BoujeeEnjinia1701/bridgepulse/cad/drawings/BRP-DWG-001.pdf

CONCEPT, NOT FOR FABRICATION | BridgePulse · github.com/BoujeeEnjinia1701/bridgepulse

FRONT VIEW

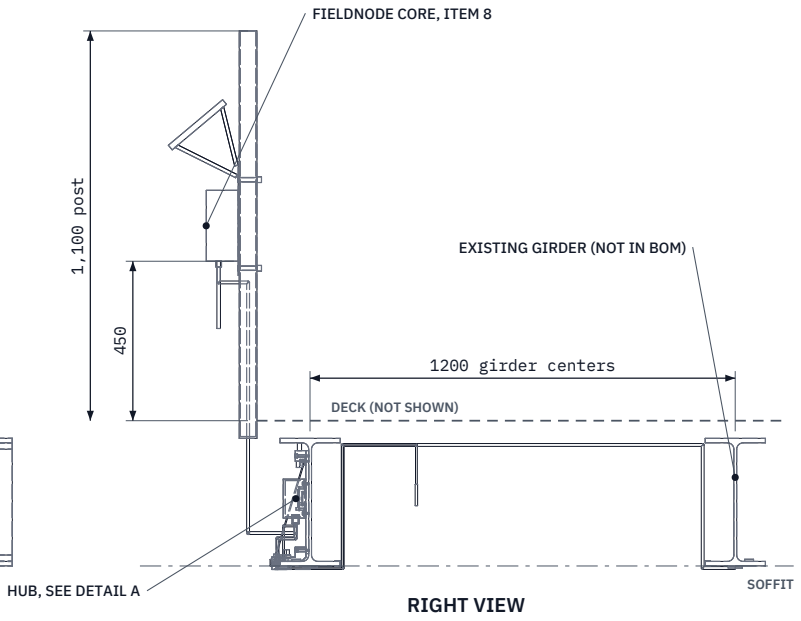
[picture p7: figure]
RIGHT VIEW; SOFFIT; DECK (NOT SHOWN); 1200 girder centers; 1,100 post; FIELDNODE CORE, ITEM 8; EXISTING GIRDER (NOT IN BOM); HUB, SEE DETAIL A

Scale 1:20; looking at the front (along +Y)

Scale 1:20; looking at the right side (along -X)

DETAIL A: HUB ON SOUTH GIRDER
Right view, scale 1:4

### PRELIMINARY, NOT FOR FABRICATION

MIDSPAN

DECK AND HANDRAILS OMITTED FOR CLARITY; HUB AND FIELDNODE ON THE -Y (SOUTH) SIDE

159

LANYARD GIRDER CLAMP, ITEM 4

3 MM STAINLESS WIRE LANYARD

291 plate

190 hub center

72

CLAMP JAW, 10 BELOW SOFFIT

HUB, ITEMS 1 TO 3

PLATE, ITEM 4

M12 JACK SCREW

LANYARD PAD EYE

ISOMETRIC VIEW
Not to scale; deck omitted; seen from the front right and above, about 30 deg elevation

MAIN DIMENSIONS AND INTERFACES (MM)
Hub 170 x 64 x 110 IP67, 9 inside the flange tip line
Plate 200 x 291 x 8 Al on the web, 22 clear of flanges; no drilling
Foot clamps +/-76; M12 jack; lanyard clamp at -275, 159 clear
Gauge covers under each flange at midspan; 10 max below soffit (R9: 15) FieldNode on the post, base 450 above deck; M12 5-pin, RS-485, 5 V Probes (item 6) TMP1826 class, 7 dia sheaths; steel on flange, air in shade Example girders IPE 360 class at 1200 centers, span 6,400
Third-angle; front view from -Y; 800 segment at midspan (x = 0)
REV | DESCRIPTION | DATE | BY
P1 | Preliminary GA for TRL 3 (from cad/src/model.py) | 2026-09-25 | AC
P2 | Probe note per BRP-DDR-002 | 2026-09-25 | AC
P3 | Far gauge cable clear of bottom flanges per BRP-DDR-003 | 2026-09-27 | AC
P4 | Layout and labels tidied | 2026-09-30 | AC
P5 | Made constructable per BRP-DDR-004 | 2026-09-30 | AC
P6 | Lanyard, pad eye and girder clamp per BRP-DEC-001 | 2026-10-02 | AC
BRIDGEPULSE | github.com/BoujeeEnjinia1701/bridgepulse

## General arrangement at midspan

DRAWING NO.
BRP-DWG-001

REV
P6

SHEET
1 of 1

SIZE

## ANSI B

SCALE
1:20

UNITS
mm
PROJECTION | DATE
2026-10-02

DRAWN
Amish Chadha

MATERIAL / NOTES
6061 Al plate; bought-in parts per bom/bom.csv. PRELIMINARY, NOT FOR FABRICATION
Licensed CERN-OHL-S-2.0 · Design Molecule Lab · designmolecule.com | Generated from cad/src; do not edit by hand
