BoujeeEnjinia1701/bridgepulse/cad/drawings/BRP-DWG-101.pdf

BUILD PLAN SKETCH, PLAN NOT YET BUILT BridgePulse · github.com/BoujeeEnjinia1701/bridgepulse

FRONT VIEW
Scale 1:5; looking at the front (along +Y)

TOP VIEW
Scale 1:5; looking down (along -Z)

RIGHT VIEW
Scale 1:5; looking at the right side (along -X)

200

8 291

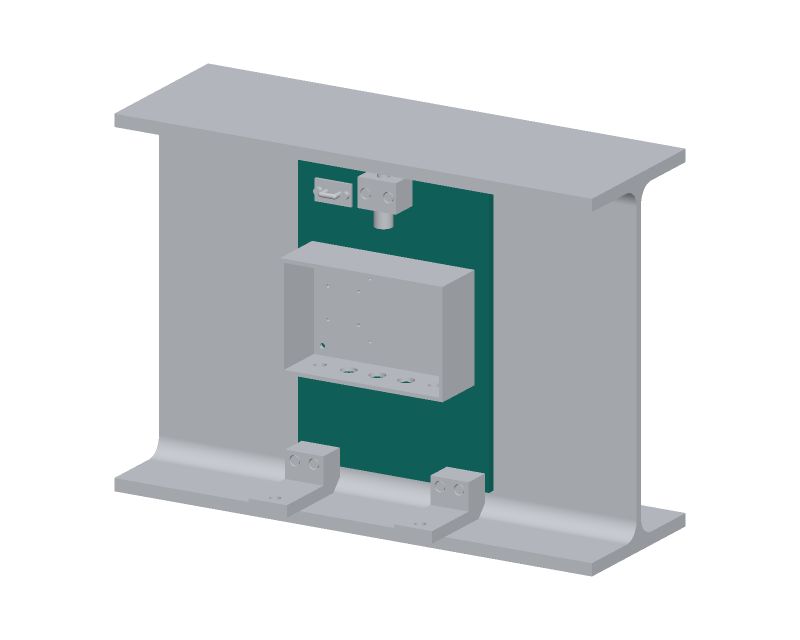
[picture p8: figure]

WHERE IT GOES
This part in colour, its neighbours in grey

HOW TO MAKE IT AND HOW IT FITS
Blank 200 x 290.6 x 8 mm: the girder's clear web height
(334.6 mm on IPE 360) less 22 mm at each end, to clear the root fillets. Front face: the face the hub sits on. Heights from the bottom edge, sideways from the centre line. All holes go right through.
Hub screws: four M5 tapped (drill 4.2) at 72 each side,
113.3 and 197.3 up.
Foot block screws: four M6 tapped (drill 5.0) at 66 and 86 each side, 9 up.
Jack block screws: two M6 tapped at 12 each side, 275.6 up. Pad eye screws: two M5 tapped at 48 and 76 left of centre,
260.6 up (left side only).
Deburr; break the edges 0.5 mm; hard anodize (it also insulates).
Check: lay the foot blocks and jack block on it and look through each hole.
REV | DESCRIPTION | DATE | BY
P1 | Making sketch for the prototype build plan | 2026-09-30 | AC
P2 | Pad eye holes replace the lanyard hole (BRP-DEC-001) | 2026-10-02 | AC
BRIDGEPULSE | github.com/BoujeeEnjinia1701/bridgepulse

## BridgePulse mounting plate: making sketch

DRAWING NO.
BRP-DWG-101

REV
P2

SHEET
1 of 1

SIZE

## ANSI B

SCALE
1:5

UNITS
mm
PROJECTION | DATE
2026-10-02

DRAWN
Amish Chadha

MATERIAL / NOTES
6061 aluminium plate 8 mm, hard anodized after machining
Licensed CERN-OHL-S-2.0 · Design Molecule Lab · designmolecule.com | Generated from cad/src; do not edit by hand
