BoujeeEnjinia1701/bridgepulse/cad/drawings/BRP-DWG-102.pdf

BUILD PLAN SKETCH, PLAN NOT YET BUILT BridgePulse · github.com/BoujeeEnjinia1701/bridgepulse

FRONT VIEW
Scale 1:2; looking at the front (along +Y)

TOP VIEW
Scale 1:2; looking down (along -Z)

RIGHT VIEW
Scale 1:2; looking at the right side (along -X)

40

96 40

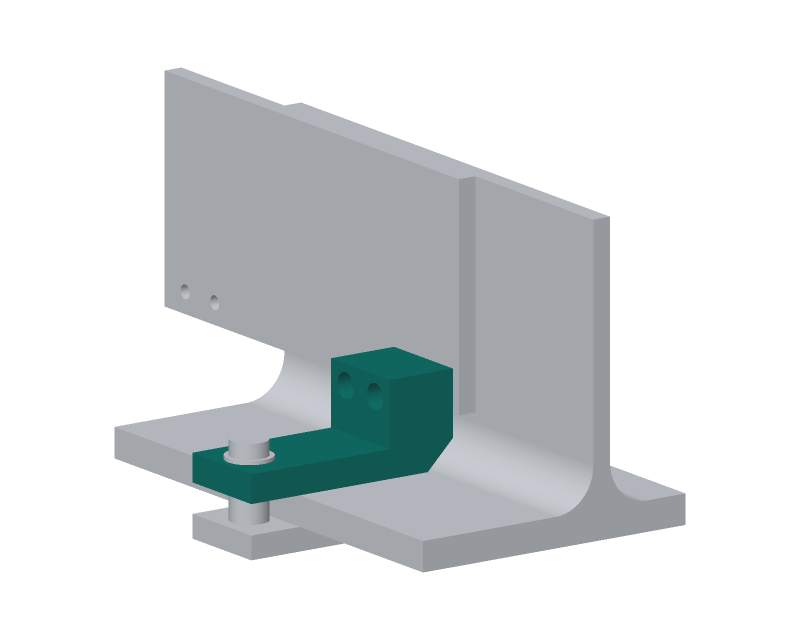
[picture p43: figure]

WHERE IT GOES
This part in colour, its neighbours in grey

HOW TO MAKE IT AND HOW IT FITS
Make two, both the same. Saw a 40 mm slice off 100 x 40 mm bar and square it to 96 long, 40 tall and 40 wide.
Saw out a step 66 long and 28 deep, leaving a tall end 30 long and
a tail 12 thick. The tall end's back face goes on the plate.
File a 12 x 12 mm 45 degree chamfer along the bottom of the back face: it keeps the block off the girder's root fillet.
Tall end: two 6.6 mm holes through, 10 each side of centre, 31 up; counterbore 11 mm, 6.5 deep, from the front for M6 cap screws.
Tail: one 11 mm hole, 13 from its end, on the centre line.
Fit: back face flat on the plate front, bottom on the flange top, tail out past the flange tip. Two M6 x 30 screws into the plate. Check: on a flange offcut it sits flat with no rock at the fillet.
REV | DESCRIPTION | DATE | BY
P1 | Making sketch for the prototype build plan | 2026-09-30 | AC
BRIDGEPULSE | github.com/BoujeeEnjinia1701/bridgepulse

## BridgePulse foot block (make 2): making sketch

DRAWING NO.
BRP-DWG-102

REV
P1

SHEET
1 of 1

SIZE

## ANSI B

SCALE
1:2

UNITS
mm
PROJECTION | DATE
2026-09-30

DRAWN
Amish Chadha

MATERIAL / NOTES
6061 aluminium flat bar 100 x 40 mm, hard anodized
Licensed CERN-OHL-S-2.0 · Design Molecule Lab · designmolecule.com | Generated from cad/src; do not edit by hand
