BoujeeEnjinia1701/bridgepulse/cad/drawings/BRP-DWG-103.pdf

BUILD PLAN SKETCH, PLAN NOT YET BUILT BridgePulse · github.com/BoujeeEnjinia1701/bridgepulse

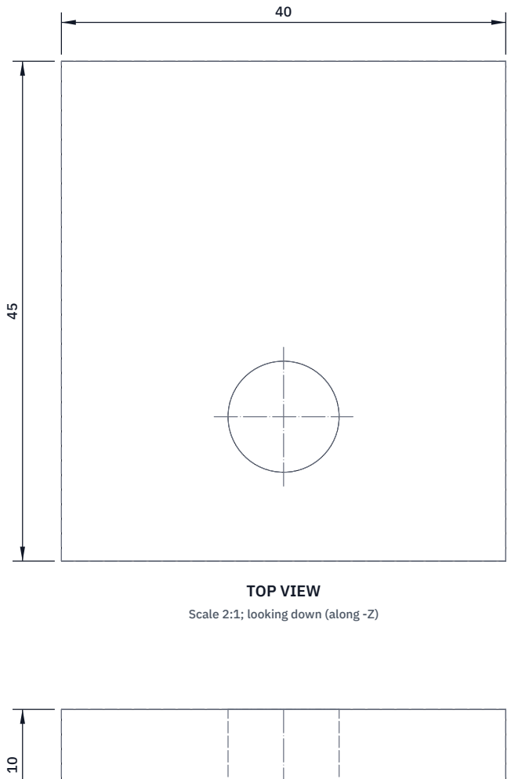
[picture p44: figure]
TOP VIEW; Scale 2:1; looking down (along -Z)

FRONT VIEW
Scale 2:1; looking at the front (along +Y)

RIGHT VIEW
Scale 2:1; looking at the right side (along -X)

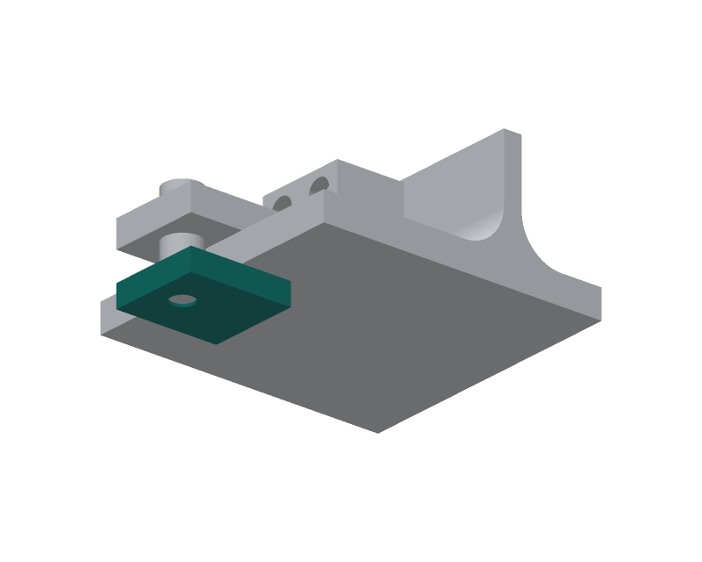
[picture p45: figure]

WHERE IT GOES
This part in colour, its neighbours in grey

HOW TO MAKE IT AND HOW IT FITS
Jaw: cut two 45 mm lengths of 40 x 10 mm steel flat bar; deburr.
Drill 8.5 mm and tap M10 right through, 13 from one end, on the centre line. Break the edges; zinc plate or paint with zinc-rich primer.
Packer: cut two lengths of steel tube, 16 mm outside, 10.5 mm or more inside, 12.2 long: the flange thickness less 0.5 mm.
Measure the real flange first and cut to suit; square the ends.
Fit: the jaw goes under the flange, 22 mm in from the tip, its tapped end out past the tip. The packer stands on the jaw beside the tip. The M10 x 35 bolt comes down through the foot block tail and the packer into the jaw; it must not stand out below the jaw.
Check: the bolt runs into the jaw by hand, and its tip stops
1 mm or more short of the jaw's underside.
REV | DESCRIPTION | DATE | BY
P1 | Making sketch for the prototype build plan | 2026-09-30 | AC
BRIDGEPULSE | github.com/BoujeeEnjinia1701/bridgepulse

## BridgePulse clamp jaw and packer (make 2 each): making sketch

DRAWING NO.
BRP-DWG-103

REV
P1

SHEET
1 of 1

SIZE

## ANSI B

SCALE
2:1

UNITS
mm
PROJECTION | DATE
2026-09-30

DRAWN
Amish Chadha

MATERIAL / NOTES
Steel flat bar 40 x 10 mm, zinc plated; packer: steel tube 16 mm outside
Licensed CERN-OHL-S-2.0 · Design Molecule Lab · designmolecule.com | Generated from cad/src; do not edit by hand
