BoujeeEnjinia1701/bridgepulse/cad/drawings/BRP-DWG-104.pdf

BUILD PLAN SKETCH, PLAN NOT YET BUILT BridgePulse · github.com/BoujeeEnjinia1701/bridgepulse

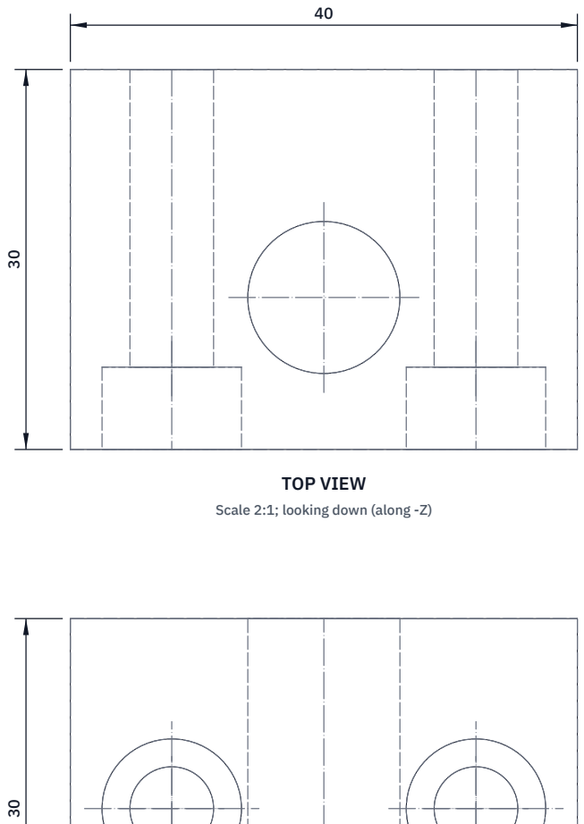
[picture p46: figure]
TOP VIEW; Scale 2:1; looking down (along -Z)
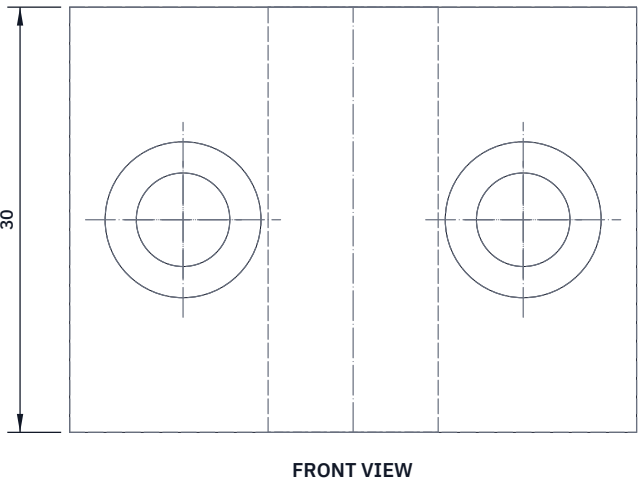
[picture p47: figure]
FRONT VIEW

Scale 2:1; looking at the front (along +Y)

RIGHT VIEW
Scale 2:1; looking at the right side (along -X)

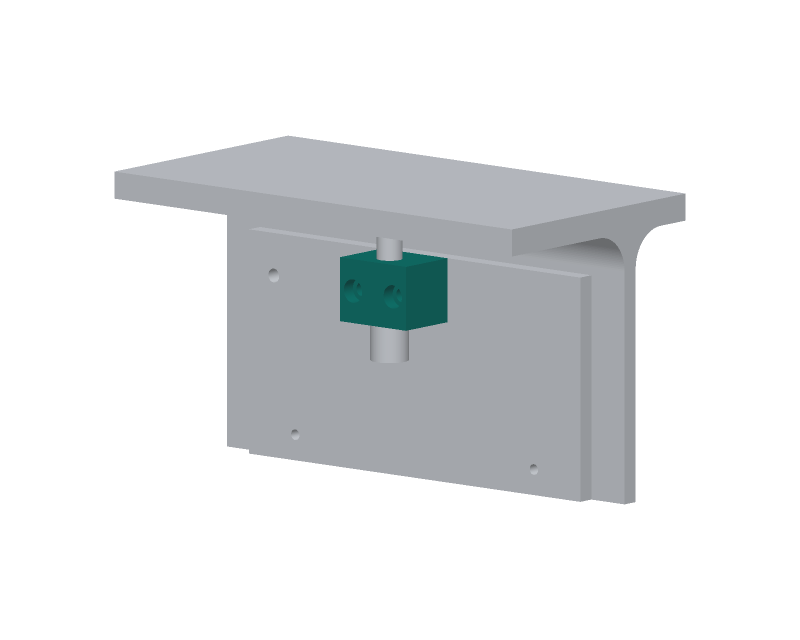
[picture p48: figure]

WHERE IT GOES
This part in colour, its neighbours in grey

HOW TO MAKE IT AND HOW IT FITS
Cut 30 mm off 40 x 30 mm bar: a block 40 wide, 30 deep, 30 tall.
The 40 x 30 face that goes on the plate is the back face.
Jack hole: drill 10.2 mm top to bottom, 18 from the back face, on the centre line, square to the top; tap M12 the full 30 mm.
Fixing holes: two 6.6 mm holes front to back, 12 each side of centre,
half way up; counterbore 11 mm, 6.5 deep, from the front.
Fit: back face on the plate front, top flush with the plate's top edge; two M6 x 30 cap screws into the plate.
The M12 x 70 jack screw goes up through it, head below, lock nut under the block; its end bears on the top flange 22 mm above. Check: the jack screw turns freely through the full thread.
REV | DESCRIPTION | DATE | BY
P1 | Making sketch for the prototype build plan | 2026-09-30 | AC
BRIDGEPULSE | github.com/BoujeeEnjinia1701/bridgepulse

## BridgePulse jack block: making sketch

DRAWING NO.
BRP-DWG-104

REV
P1

SHEET
1 of 1

SIZE

## ANSI B

SCALE
2:1

UNITS
mm
PROJECTION | DATE
2026-09-30

DRAWN
Amish Chadha

MATERIAL / NOTES
6061 aluminium flat bar 40 x 30 mm
Licensed CERN-OHL-S-2.0 · Design Molecule Lab · designmolecule.com | Generated from cad/src; do not edit by hand
