BoujeeEnjinia1701/bridgepulse/cad/drawings/BRP-DWG-105.pdf

BUILD PLAN SKETCH, PLAN NOT YET BUILT BridgePulse · github.com/BoujeeEnjinia1701/bridgepulse

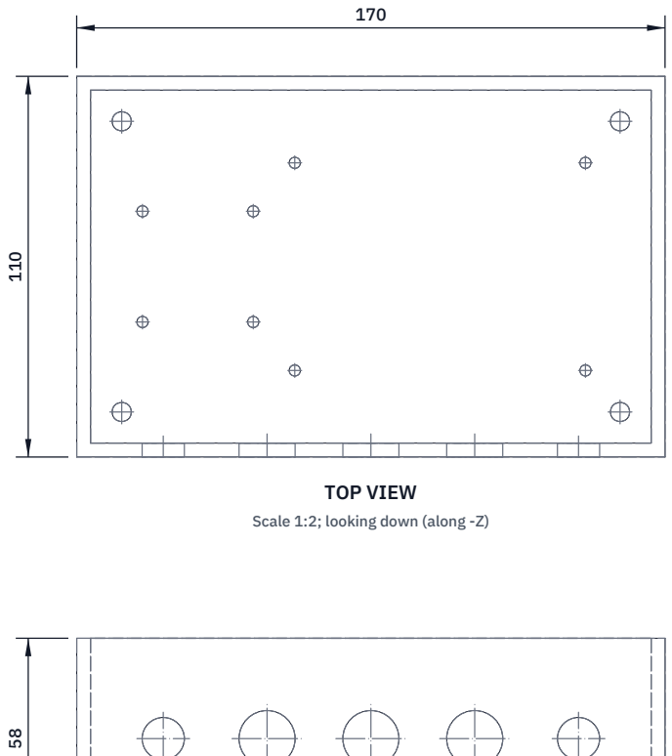
[picture p49: figure]
TOP VIEW; Scale 1:2; looking down (along -Z)

FRONT VIEW
Scale 1:2; looking at the front (along +Y)

RIGHT VIEW
Scale 1:2; looking at the right side (along -X)

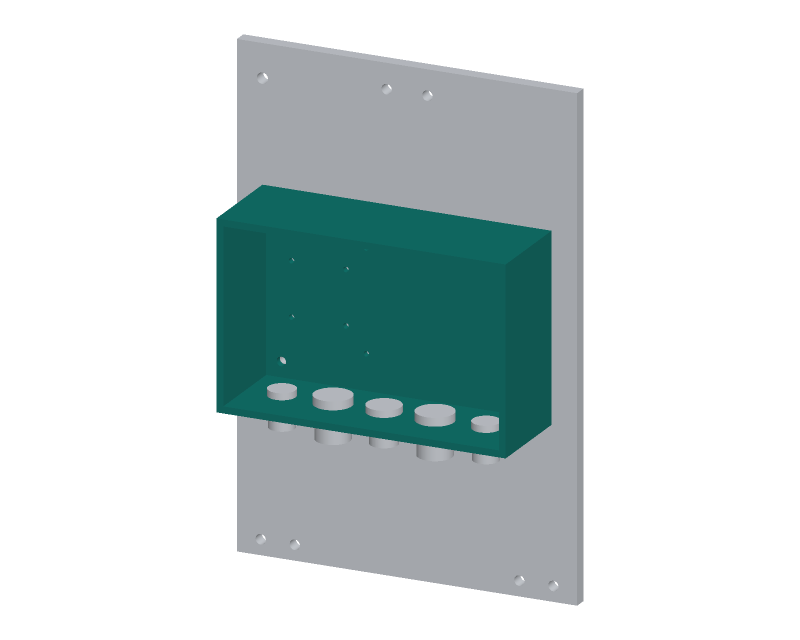
[picture p50: figure]

WHERE IT GOES
This part in colour, its neighbours in grey

HOW TO MAKE IT AND HOW IT FITS
Drawn lying on its back with the lid off: the top view looks into the box
at the base; the front view shows the bottom face.
Base, from the base's centre: four 5.5 mm holes at 72 each side, 42 above and below (the hub screws).
Base: eight 3.2 mm holes for the board spacers and standoffs, countersunk outside so the M3 heads sit flush (positions in the hub holes picture). Bottom face, on its centre line, sideways from the centre:
60 left: 12.5 mm (steel probe gland, M12)
30 left and 30 right: 16.5 mm (gauge glands, M16)
centre: 16.5 mm (M12 panel connector, M16 thread)
60 right: 12.5 mm (air probe gland, M12). Left and right as seen from the lid. Deburr inside and out; clean the lid gasket groove of chips.
REV | DESCRIPTION | DATE | BY
P1 | Making sketch for the prototype build plan | 2026-09-30 | AC
BRIDGEPULSE | github.com/BoujeeEnjinia1701/bridgepulse

## BridgePulse hub enclosure: drilling sketch

DRAWING NO.
BRP-DWG-105

REV
P1

SHEET
1 of 1

SIZE

## ANSI B

SCALE
1:2

UNITS
mm
PROJECTION | DATE
2026-09-30

DRAWN
Amish Chadha

MATERIAL / NOTES
Bought die-cast aluminium box, IP67, 170 x 64 x 110 mm
Licensed CERN-OHL-S-2.0 · Design Molecule Lab · designmolecule.com | Generated from cad/src; do not edit by hand
