BoujeeEnjinia1701/bridgepulse/cad/drawings/BRP-DWG-106.pdf

BUILD PLAN SKETCH, PLAN NOT YET BUILT BridgePulse · github.com/BoujeeEnjinia1701/bridgepulse

FRONT VIEW
Scale 2:1; looking at the front (along +Y)

TOP VIEW
Scale 2:1; looking down (along -Z)

RIGHT VIEW
Scale 2:1; looking at the right side (along -X)

40

25 6

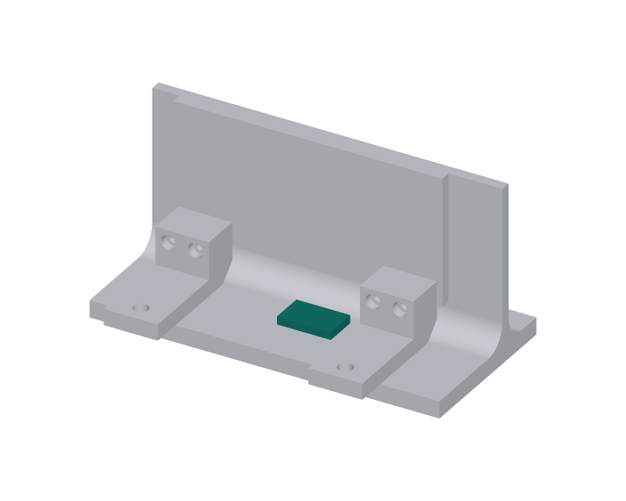
[picture p51: figure]

WHERE IT GOES
This part in colour, its neighbours in grey

HOW TO MAKE IT AND HOW IT FITS
Cut two 40 mm lengths of 25 x 6 mm steel flat bar.
Grind one 40 x 25 face flat and clean to bright metal; this is where the dummy gauge goes. Round the edges lightly.
Bond a gauge of the same type and batch as the active gauge to the middle of the bright face, the same way round as the active gauge. Solder its leads, coat it with the same coating as the active gauge, and fit a cover patch.
Fit: set it on the flange top, its centre 35 out from the web face,
on a bed of neutral-cure silicone, so it takes the steel's
temperature but none of its strain. Never glue it rigidly.
Check: the coupon can be lifted by hand once the silicone has cured.
REV | DESCRIPTION | DATE | BY
P1 | Making sketch for the prototype build plan | 2026-09-30 | AC
BRIDGEPULSE | github.com/BoujeeEnjinia1701/bridgepulse

## BridgePulse dummy gauge coupon (make 2): making sketch

DRAWING NO.
BRP-DWG-106

REV
P1

SHEET
1 of 1

SIZE

## ANSI B

SCALE
2:1

UNITS
mm
PROJECTION | DATE
2026-09-30

DRAWN
Amish Chadha

MATERIAL / NOTES
Steel flat bar 25 x 6 mm, the same steel grade as the girder if known
Licensed CERN-OHL-S-2.0 · Design Molecule Lab · designmolecule.com | Generated from cad/src; do not edit by hand
