BoujeeEnjinia1701/bridgepulse/cad/drawings/BRP-DWG-107.pdf

BUILD PLAN SKETCH, PLAN NOT YET BUILT BridgePulse · github.com/BoujeeEnjinia1701/bridgepulse

FRONT VIEW
Scale 2:1; looking at the front (along +Y)

TOP VIEW
Scale 2:1; looking down (along -Z)

RIGHT VIEW
Scale 2:1; looking at the right side (along -X)

60

7 7

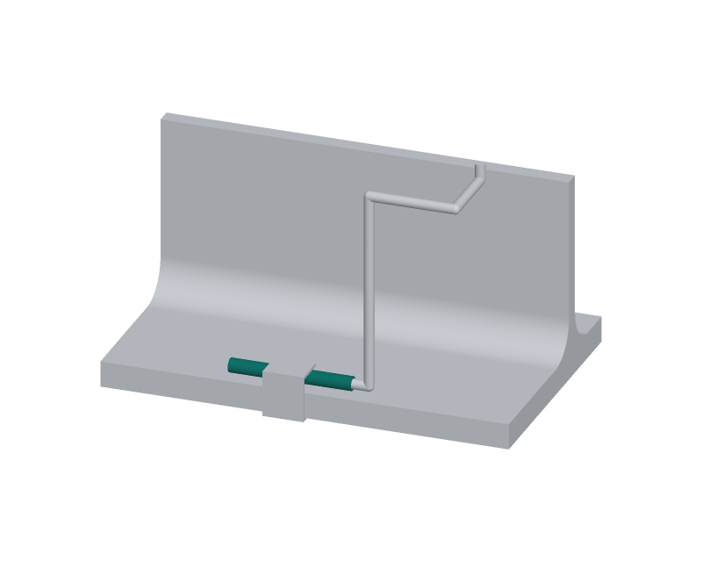
[picture p52: figure]

WHERE IT GOES
This part in colour, its neighbours in grey

HOW TO MAKE IT AND HOW IT FITS
Make two, both the same. Solder the sensor carrier to a 3-core sealed outdoor lead (1-Wire: data, ground and supply), 2 m for the steel probe and 3 m for the air probe.
Push the carrier to the closed end of the sheath, sensor face down, with a dab of thermal paste between the sensor and the sheath end. Fill the sheath with potting epoxy from the closed end up, with no air pockets; fit heat-shrink with adhesive over the sheath mouth. Steel probe: lies on the bottom flange top, 6.5 from the tip, held by a spring-steel flange clip with thermal paste under it.
Air probe: hangs on its lead between the girders, in shade.
Check each probe in ice water: 0 degC within 0.5 degC (R5).
REV | DESCRIPTION | DATE | BY
P1 | Making sketch for the prototype build plan | 2026-09-30 | AC
BRIDGEPULSE | github.com/BoujeeEnjinia1701/bridgepulse

## BridgePulse temperature probe (make 2): making sketch

DRAWING NO.
BRP-DWG-107

REV
P1

SHEET
1 of 1

SIZE

## ANSI B

SCALE
2:1

UNITS
mm
PROJECTION | DATE
2026-09-30

DRAWN
Amish Chadha

MATERIAL / NOTES
Stainless sheath 7 x 60 mm, TMP1826 class sensor on a carrier, potting epoxy
Licensed CERN-OHL-S-2.0 · Design Molecule Lab · designmolecule.com | Generated from cad/src; do not edit by hand
