BoujeeEnjinia1701/bridgepulse/cad/drawings/BRP-DWG-001.png

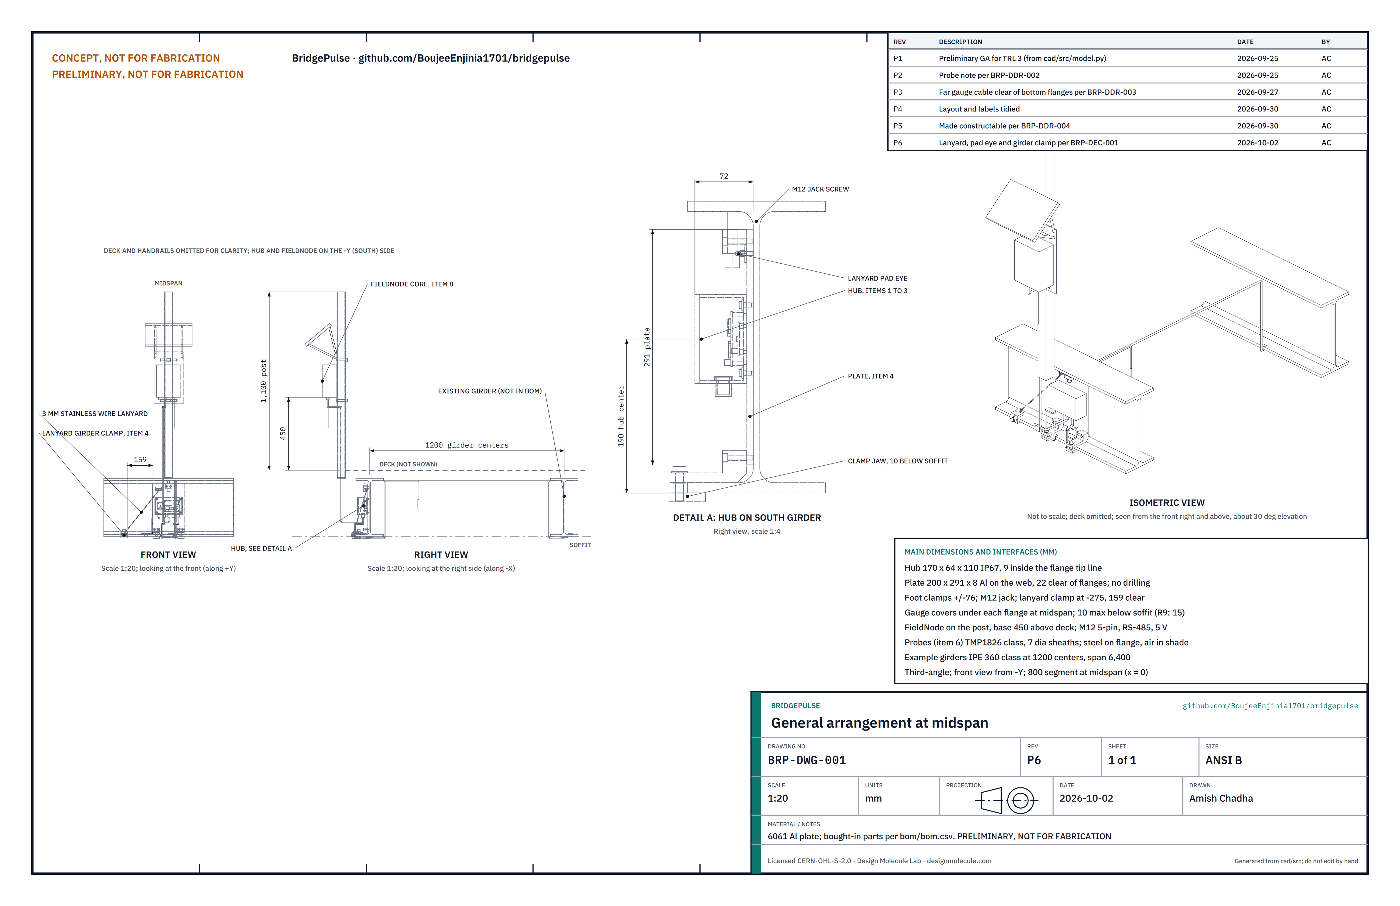
cad/drawings/BRP-DWG-001.png
