BoujeeEnjinia1701/bridgepulse/media/card.png

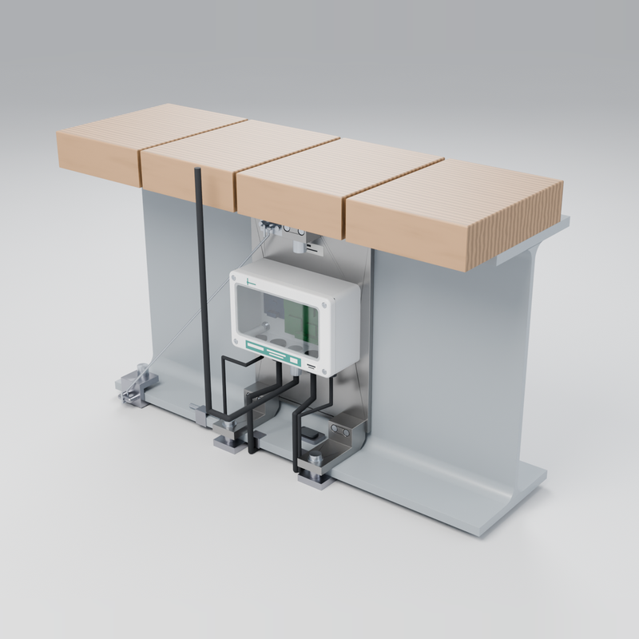
media/card.png
