BoujeeEnjinia1701/bridgepulse/media/render-detail.png

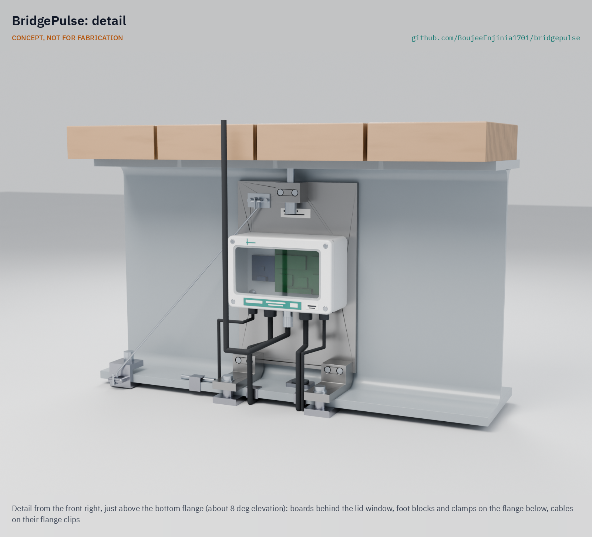
media/render-detail.png
