BoujeeEnjinia1701/bridgepulse/media/render-exploded.png

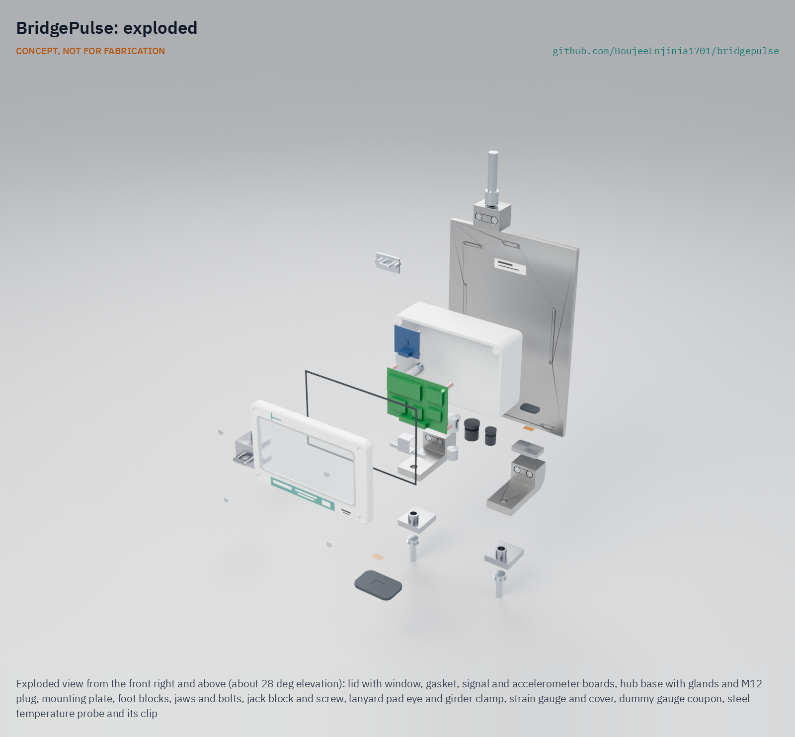
media/render-exploded.png
