BoujeeEnjinia1701/bridgepulse/media/social-preview.png

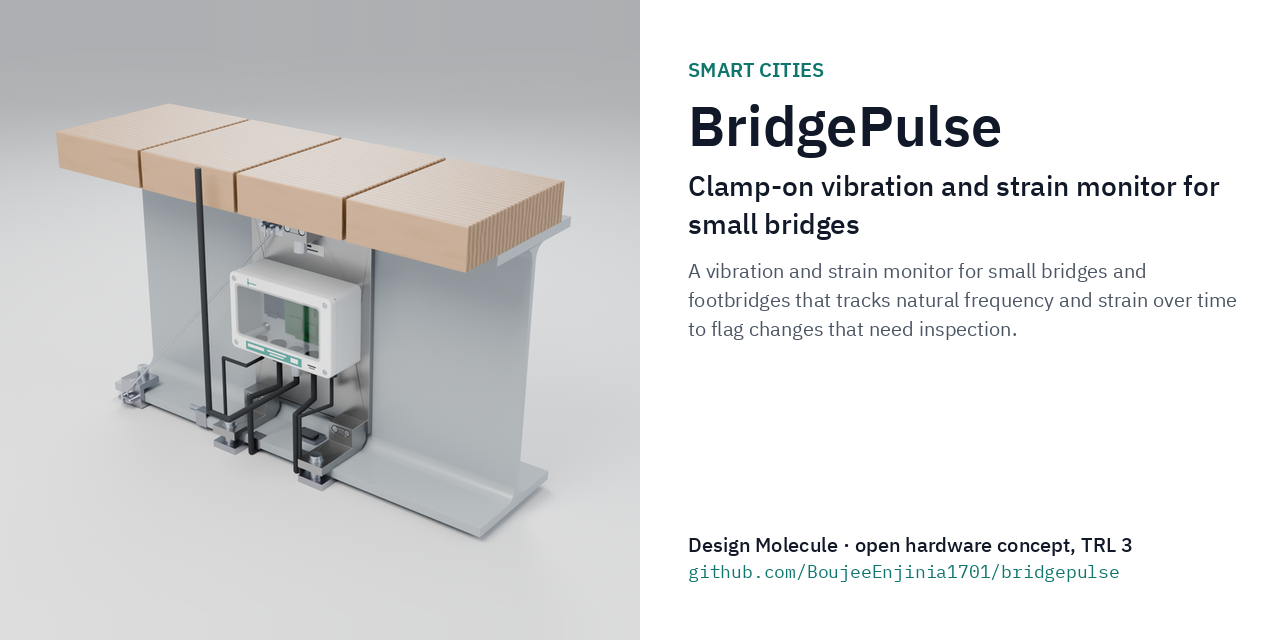
media/social-preview.png
